GenaroRdz/International-Power-and-Grid-Management/Neurnal-Network/train/Hyundai/Hyundai_005.jpg

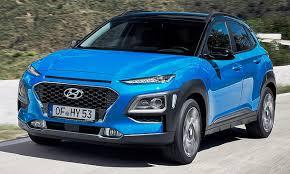
Neurnal-Network/train/Hyundai/Hyundai_005.jpg
