GenaroRdz/International-Power-and-Grid-Management/Neurnal-Network/train/MG/MG_098.jpg

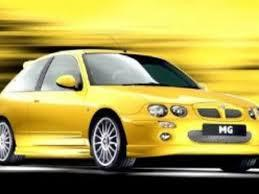
Neurnal-Network/train/MG/MG_098.jpg
