GenaroRdz/International-Power-and-Grid-Management/Neurnal-Network/graficas/mlp_size_vs_accuracy.png

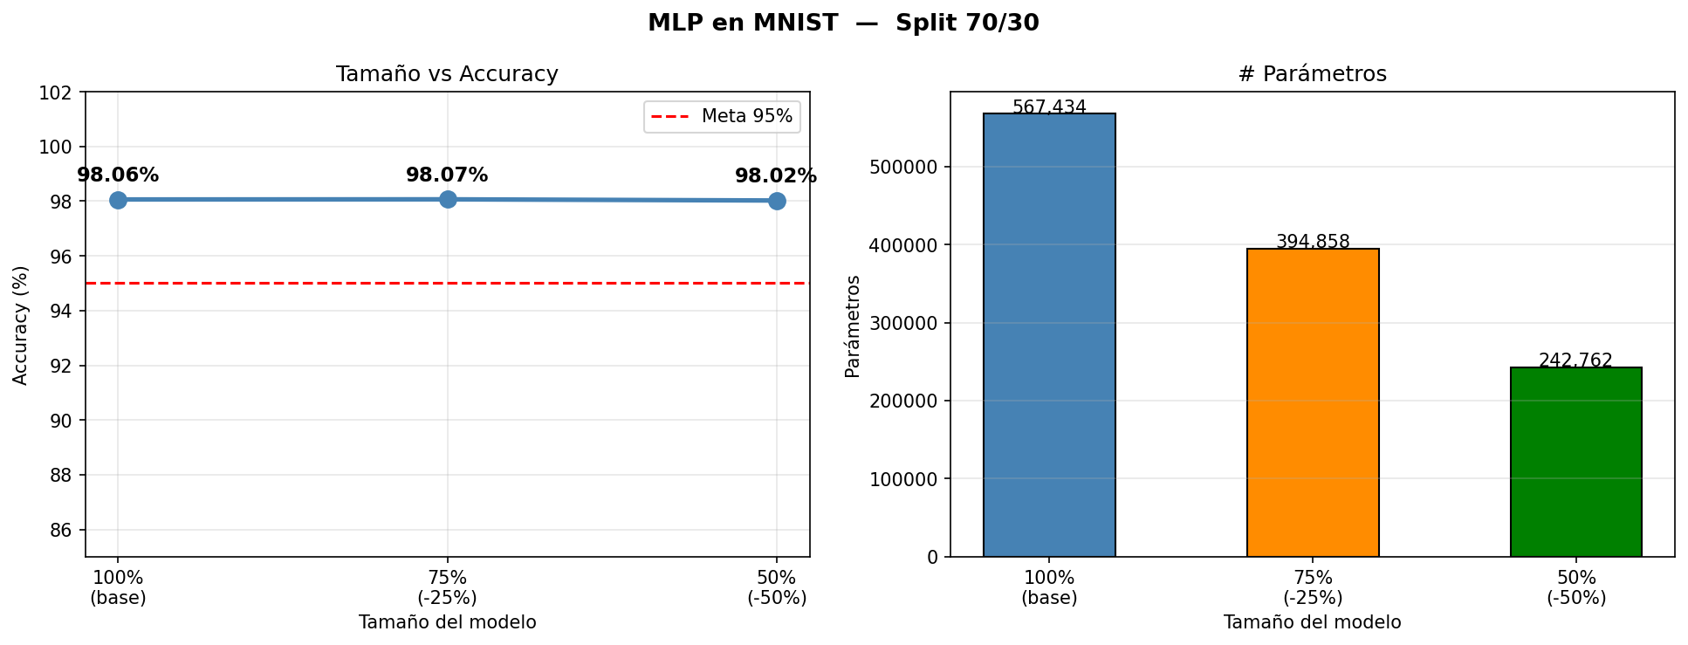
Neurnal-Network/graficas/mlp_size_vs_accuracy.png
