GenaroRdz/International-Power-and-Grid-Management/Neurnal-Network/train/Acura/Acura_019.jpg

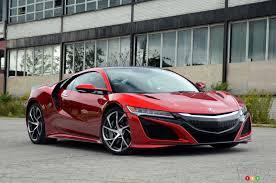
Neurnal-Network/train/Acura/Acura_019.jpg
