GenaroRdz/International-Power-and-Grid-Management/Neurnal-Network/train/Acura/Acura_023.jpg

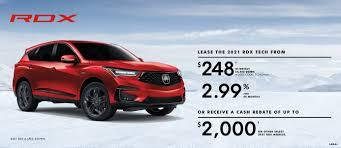
Neurnal-Network/train/Acura/Acura_023.jpg
