GenaroRdz/International-Power-and-Grid-Management/Neurnal-Network/train/Acura/Acura_026.jpg

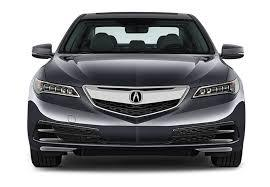
Neurnal-Network/train/Acura/Acura_026.jpg
