GenaroRdz/International-Power-and-Grid-Management/Neurnal-Network/train/Acura/Acura_050.jpg

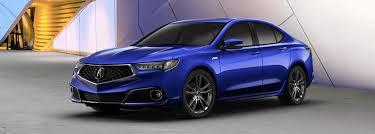
Neurnal-Network/train/Acura/Acura_050.jpg
