GenaroRdz/International-Power-and-Grid-Management/Neurnal-Network/train/Acura/Acura_061.jpg

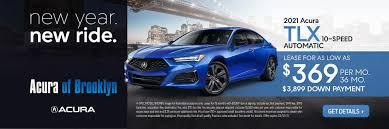
Neurnal-Network/train/Acura/Acura_061.jpg
