GenaroRdz/International-Power-and-Grid-Management/Neurnal-Network/train/Acura/Acura_066.jpg

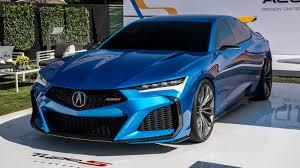
Neurnal-Network/train/Acura/Acura_066.jpg
