GenaroRdz/International-Power-and-Grid-Management/Neurnal-Network/train/Acura/Acura_078.jpg

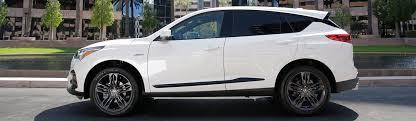
Neurnal-Network/train/Acura/Acura_078.jpg
