GenaroRdz/International-Power-and-Grid-Management/Neurnal-Network/train/Acura/Acura_080.jpg

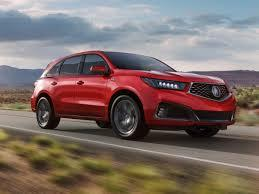
Neurnal-Network/train/Acura/Acura_080.jpg
