GenaroRdz/International-Power-and-Grid-Management/Neurnal-Network/train/Acura/Acura_088.jpg

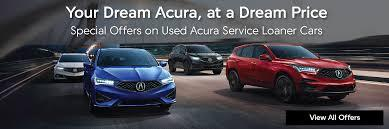
Neurnal-Network/train/Acura/Acura_088.jpg
