GenaroRdz/International-Power-and-Grid-Management/Neurnal-Network/train/Alfa Romeo/Alfa Romeo_034.jpg

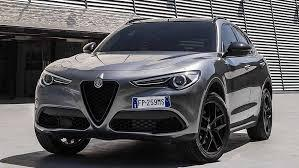
Neurnal-Network/train/Alfa Romeo/Alfa Romeo_034.jpg
