GenaroRdz/International-Power-and-Grid-Management/Neurnal-Network/train/Alfa Romeo/Alfa Romeo_074.jpg

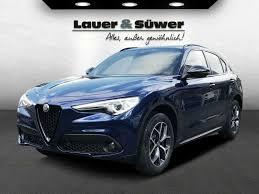
Neurnal-Network/train/Alfa Romeo/Alfa Romeo_074.jpg
