GenaroRdz/International-Power-and-Grid-Management/Neurnal-Network/train/Aston Martin/Aston Martin_030.jpg

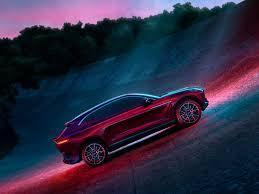
Neurnal-Network/train/Aston Martin/Aston Martin_030.jpg
