GenaroRdz/International-Power-and-Grid-Management/Neurnal-Network/train/Audi/Audi_017.jpg

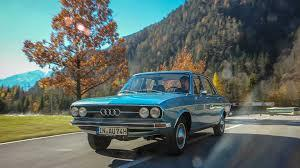
Neurnal-Network/train/Audi/Audi_017.jpg
