GenaroRdz/International-Power-and-Grid-Management/Neurnal-Network/train/Audi/Audi_038.jpg

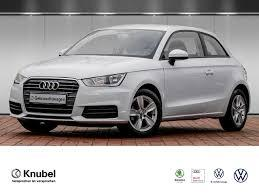
Neurnal-Network/train/Audi/Audi_038.jpg
