GenaroRdz/International-Power-and-Grid-Management/Neurnal-Network/train/Audi/Audi_059.jpg

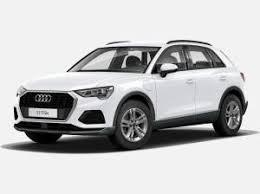
Neurnal-Network/train/Audi/Audi_059.jpg
