GenaroRdz/International-Power-and-Grid-Management/Neurnal-Network/train/Bentley/Bentley_013.jpg

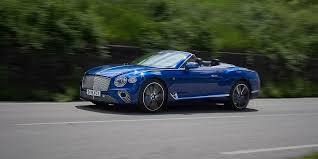
Neurnal-Network/train/Bentley/Bentley_013.jpg
