GenaroRdz/International-Power-and-Grid-Management/Neurnal-Network/train/Bentley/Bentley_045.jpg

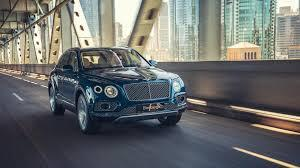
Neurnal-Network/train/Bentley/Bentley_045.jpg
