GenaroRdz/International-Power-and-Grid-Management/Neurnal-Network/train/Bentley/Bentley_058.jpg

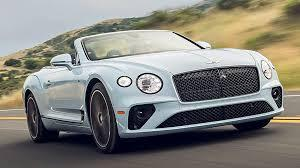
Neurnal-Network/train/Bentley/Bentley_058.jpg
