GenaroRdz/International-Power-and-Grid-Management/Neurnal-Network/train/Bentley/Bentley_075.jpg

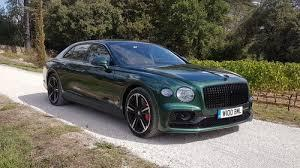
Neurnal-Network/train/Bentley/Bentley_075.jpg
