GenaroRdz/International-Power-and-Grid-Management/Neurnal-Network/train/BMW/BMW_029.jpg

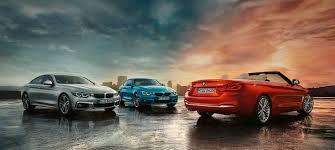
Neurnal-Network/train/BMW/BMW_029.jpg
