GenaroRdz/International-Power-and-Grid-Management/Neurnal-Network/train/BMW/BMW_037.jpg

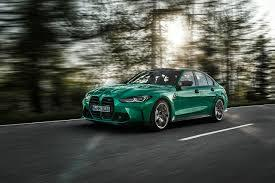
Neurnal-Network/train/BMW/BMW_037.jpg
