GenaroRdz/International-Power-and-Grid-Management/Neurnal-Network/train/BMW/BMW_071.jpg

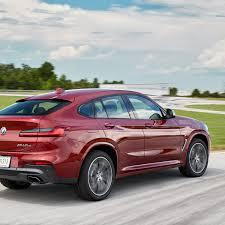
Neurnal-Network/train/BMW/BMW_071.jpg
