GenaroRdz/International-Power-and-Grid-Management/Neurnal-Network/train/Bugatti/Bugatti_005.jpg

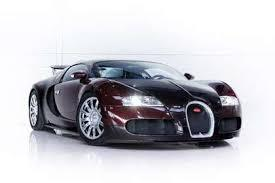
Neurnal-Network/train/Bugatti/Bugatti_005.jpg
