GenaroRdz/International-Power-and-Grid-Management/Neurnal-Network/train/Bugatti/Bugatti_016.jpg

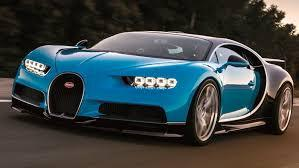
Neurnal-Network/train/Bugatti/Bugatti_016.jpg
