GenaroRdz/International-Power-and-Grid-Management/Neurnal-Network/train/Bugatti/Bugatti_018.jpg

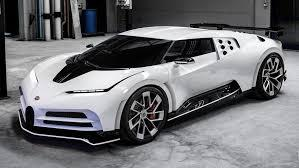
Neurnal-Network/train/Bugatti/Bugatti_018.jpg
