GenaroRdz/International-Power-and-Grid-Management/Neurnal-Network/train/Bugatti/Bugatti_038.jpg

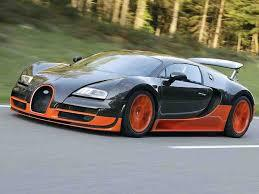
Neurnal-Network/train/Bugatti/Bugatti_038.jpg
