GenaroRdz/International-Power-and-Grid-Management/Neurnal-Network/train/Bugatti/Bugatti_048.jpg

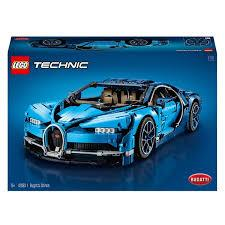
Neurnal-Network/train/Bugatti/Bugatti_048.jpg
