GenaroRdz/International-Power-and-Grid-Management/Neurnal-Network/train/Bugatti/Bugatti_087.jpg

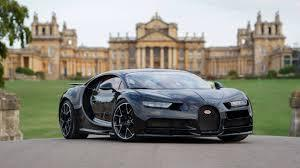
Neurnal-Network/train/Bugatti/Bugatti_087.jpg
