GenaroRdz/International-Power-and-Grid-Management/Neurnal-Network/train/Buick/Buick_023.jpg

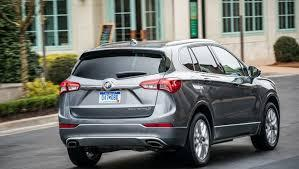
Neurnal-Network/train/Buick/Buick_023.jpg
