GenaroRdz/International-Power-and-Grid-Management/Neurnal-Network/train/Buick/Buick_024.jpg

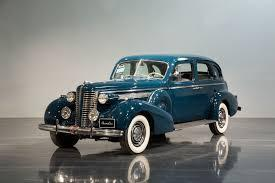
Neurnal-Network/train/Buick/Buick_024.jpg
