GenaroRdz/International-Power-and-Grid-Management/Neurnal-Network/train/Buick/Buick_026.jpg

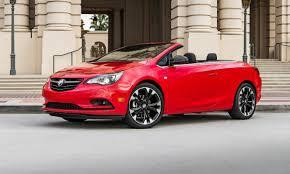
Neurnal-Network/train/Buick/Buick_026.jpg
