GenaroRdz/International-Power-and-Grid-Management/Neurnal-Network/train/Buick/Buick_034.jpg

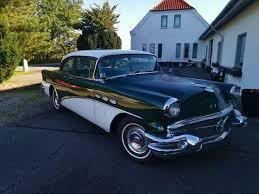
Neurnal-Network/train/Buick/Buick_034.jpg
