GenaroRdz/International-Power-and-Grid-Management/Neurnal-Network/train/Buick/Buick_044.jpg

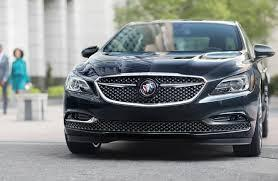
Neurnal-Network/train/Buick/Buick_044.jpg
