GenaroRdz/International-Power-and-Grid-Management/Neurnal-Network/train/Buick/Buick_053.jpg

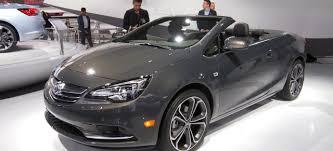
Neurnal-Network/train/Buick/Buick_053.jpg
