GenaroRdz/International-Power-and-Grid-Management/Neurnal-Network/train/Buick/Buick_087.jpg

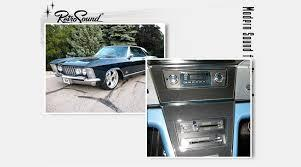
Neurnal-Network/train/Buick/Buick_087.jpg
