GenaroRdz/International-Power-and-Grid-Management/Neurnal-Network/train/Buick/Buick_091.jpg

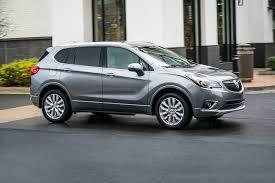
Neurnal-Network/train/Buick/Buick_091.jpg
