GenaroRdz/International-Power-and-Grid-Management/Neurnal-Network/train/Cadillac/Cadillac_010.jpg

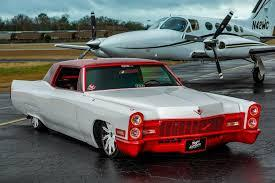
Neurnal-Network/train/Cadillac/Cadillac_010.jpg
