GenaroRdz/International-Power-and-Grid-Management/Neurnal-Network/train/Cadillac/Cadillac_023.jpg

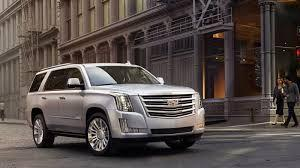
Neurnal-Network/train/Cadillac/Cadillac_023.jpg
