GenaroRdz/International-Power-and-Grid-Management/Neurnal-Network/train/Cadillac/Cadillac_036.jpg

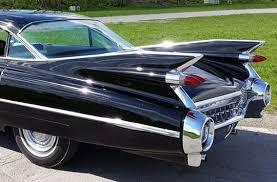
Neurnal-Network/train/Cadillac/Cadillac_036.jpg
