GenaroRdz/International-Power-and-Grid-Management/Neurnal-Network/train/Cadillac/Cadillac_062.jpg

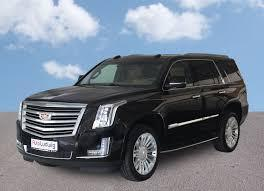
Neurnal-Network/train/Cadillac/Cadillac_062.jpg
