GenaroRdz/International-Power-and-Grid-Management/Neurnal-Network/train/Cadillac/Cadillac_063.jpg

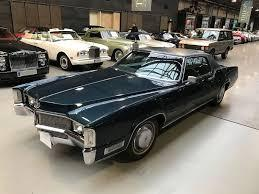
Neurnal-Network/train/Cadillac/Cadillac_063.jpg
