GenaroRdz/International-Power-and-Grid-Management/Neurnal-Network/train/Cadillac/Cadillac_084.jpg

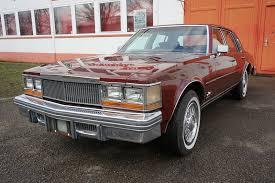
Neurnal-Network/train/Cadillac/Cadillac_084.jpg
