GenaroRdz/International-Power-and-Grid-Management/Neurnal-Network/train/Chevrolet/Chevrolet_023.jpg

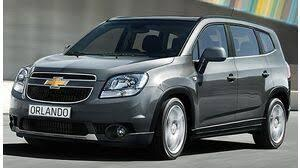
Neurnal-Network/train/Chevrolet/Chevrolet_023.jpg
