GenaroRdz/International-Power-and-Grid-Management/Neurnal-Network/train/Chevrolet/Chevrolet_030.jpg

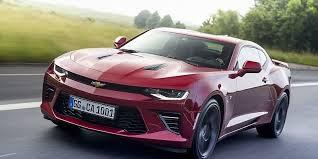
Neurnal-Network/train/Chevrolet/Chevrolet_030.jpg
