GenaroRdz/International-Power-and-Grid-Management/Neurnal-Network/train/Chevrolet/Chevrolet_035.jpg

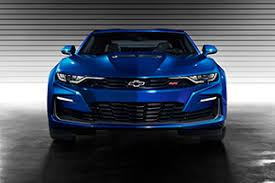
Neurnal-Network/train/Chevrolet/Chevrolet_035.jpg
