GenaroRdz/International-Power-and-Grid-Management/Neurnal-Network/train/Chevrolet/Chevrolet_060.jpg

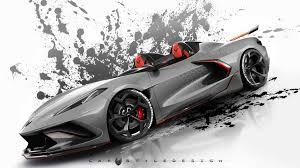
Neurnal-Network/train/Chevrolet/Chevrolet_060.jpg
