GenaroRdz/International-Power-and-Grid-Management/Neurnal-Network/train/Chevrolet/Chevrolet_083.jpg

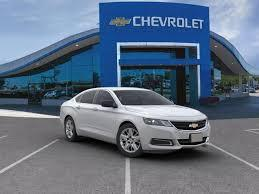
Neurnal-Network/train/Chevrolet/Chevrolet_083.jpg
