GenaroRdz/International-Power-and-Grid-Management/Neurnal-Network/train/Chevrolet/Chevrolet_084.jpg

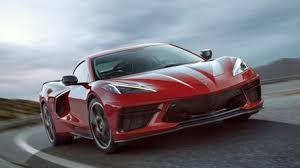
Neurnal-Network/train/Chevrolet/Chevrolet_084.jpg
