GenaroRdz/International-Power-and-Grid-Management/Neurnal-Network/train/Chrysler/Chrysler_004.jpg

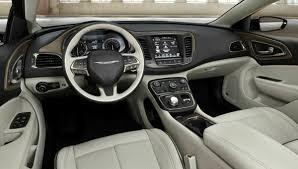
Neurnal-Network/train/Chrysler/Chrysler_004.jpg
