GenaroRdz/International-Power-and-Grid-Management/Neurnal-Network/train/Chrysler/Chrysler_086.jpg

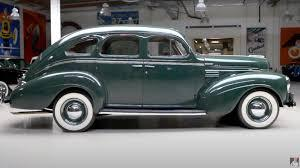
Neurnal-Network/train/Chrysler/Chrysler_086.jpg
