GenaroRdz/International-Power-and-Grid-Management/Neurnal-Network/train/Citroen/Citroen_018.jpg

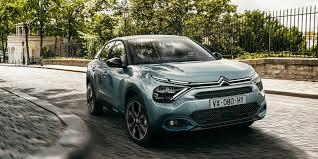
Neurnal-Network/train/Citroen/Citroen_018.jpg
