GenaroRdz/International-Power-and-Grid-Management/Neurnal-Network/train/Citroen/Citroen_023.jpg

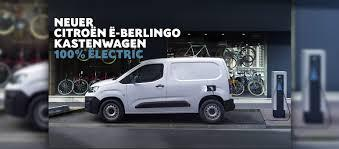
Neurnal-Network/train/Citroen/Citroen_023.jpg
