GenaroRdz/International-Power-and-Grid-Management/Neurnal-Network/train/Citroen/Citroen_032.jpg

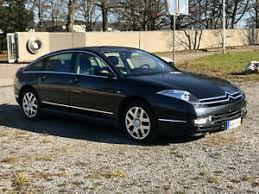
Neurnal-Network/train/Citroen/Citroen_032.jpg
