GenaroRdz/International-Power-and-Grid-Management/Neurnal-Network/train/Citroen/Citroen_034.jpg

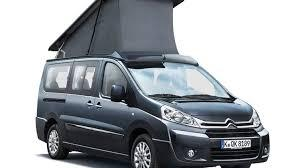
Neurnal-Network/train/Citroen/Citroen_034.jpg
