GenaroRdz/International-Power-and-Grid-Management/Neurnal-Network/train/Citroen/Citroen_036.jpg

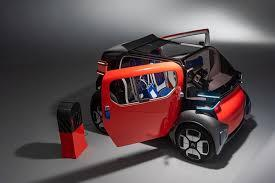
Neurnal-Network/train/Citroen/Citroen_036.jpg
