GenaroRdz/International-Power-and-Grid-Management/Neurnal-Network/train/Citroen/Citroen_077.jpg

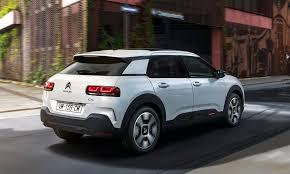
Neurnal-Network/train/Citroen/Citroen_077.jpg
