GenaroRdz/International-Power-and-Grid-Management/Neurnal-Network/train/Citroen/Citroen_078.jpg

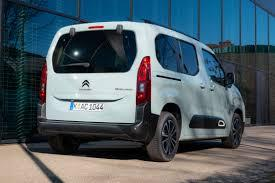
Neurnal-Network/train/Citroen/Citroen_078.jpg
