GenaroRdz/International-Power-and-Grid-Management/Neurnal-Network/train/Daewoo/Daewoo_008.jpg

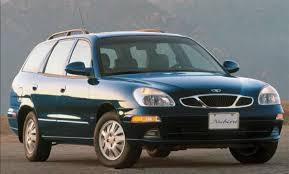
Neurnal-Network/train/Daewoo/Daewoo_008.jpg
