GenaroRdz/International-Power-and-Grid-Management/Neurnal-Network/train/Daewoo/Daewoo_037.jpg

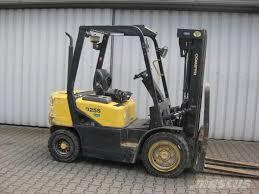
Neurnal-Network/train/Daewoo/Daewoo_037.jpg
