GenaroRdz/International-Power-and-Grid-Management/Neurnal-Network/train/Daewoo/Daewoo_059.jpg

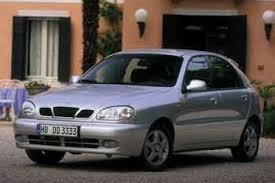
Neurnal-Network/train/Daewoo/Daewoo_059.jpg
