GenaroRdz/International-Power-and-Grid-Management/Neurnal-Network/train/Daewoo/Daewoo_086.jpg

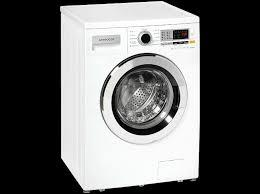
Neurnal-Network/train/Daewoo/Daewoo_086.jpg
