GenaroRdz/International-Power-and-Grid-Management/Neurnal-Network/train/Daewoo/Daewoo_088.jpg

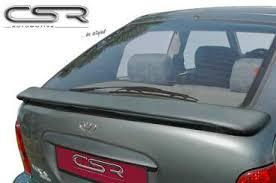
Neurnal-Network/train/Daewoo/Daewoo_088.jpg
