GenaroRdz/International-Power-and-Grid-Management/Neurnal-Network/train/Dodge/Dodge_002.jpg

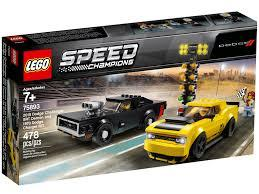
Neurnal-Network/train/Dodge/Dodge_002.jpg
