GenaroRdz/International-Power-and-Grid-Management/Neurnal-Network/train/Dodge/Dodge_019.jpg

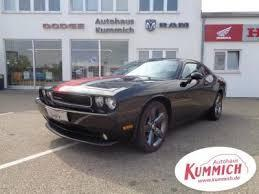
Neurnal-Network/train/Dodge/Dodge_019.jpg
