GenaroRdz/International-Power-and-Grid-Management/Neurnal-Network/train/Dodge/Dodge_027.jpg

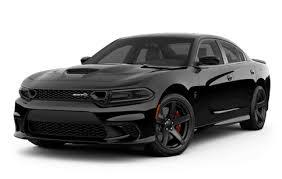
Neurnal-Network/train/Dodge/Dodge_027.jpg
