GenaroRdz/International-Power-and-Grid-Management/Neurnal-Network/train/Dodge/Dodge_032.jpg

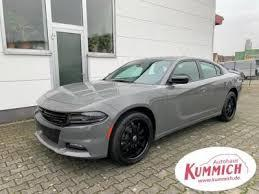
Neurnal-Network/train/Dodge/Dodge_032.jpg
