GenaroRdz/International-Power-and-Grid-Management/Neurnal-Network/train/Dodge/Dodge_049.jpg

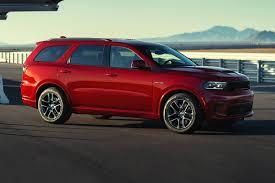
Neurnal-Network/train/Dodge/Dodge_049.jpg
