GenaroRdz/International-Power-and-Grid-Management/Neurnal-Network/train/Dodge/Dodge_055.jpg

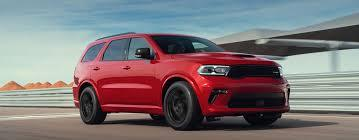
Neurnal-Network/train/Dodge/Dodge_055.jpg
