GenaroRdz/International-Power-and-Grid-Management/Neurnal-Network/train/Dodge/Dodge_057.jpg

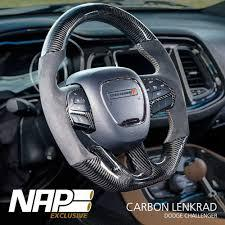
Neurnal-Network/train/Dodge/Dodge_057.jpg
