GenaroRdz/International-Power-and-Grid-Management/Neurnal-Network/train/Dodge/Dodge_060.jpg

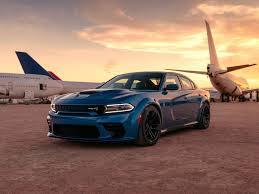
Neurnal-Network/train/Dodge/Dodge_060.jpg
