GenaroRdz/International-Power-and-Grid-Management/Neurnal-Network/train/Dodge/Dodge_066.jpg

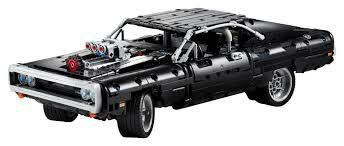
Neurnal-Network/train/Dodge/Dodge_066.jpg
