GenaroRdz/International-Power-and-Grid-Management/Neurnal-Network/train/Dodge/Dodge_072.jpg

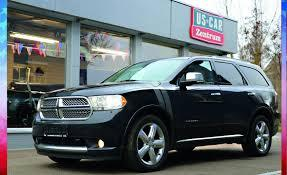
Neurnal-Network/train/Dodge/Dodge_072.jpg
