GenaroRdz/International-Power-and-Grid-Management/Neurnal-Network/train/Ferrari/Ferrari_000.jpg

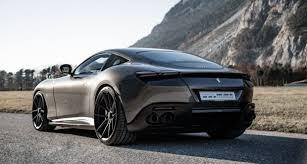
Neurnal-Network/train/Ferrari/Ferrari_000.jpg
