GenaroRdz/International-Power-and-Grid-Management/Neurnal-Network/train/Ferrari/Ferrari_005.jpg

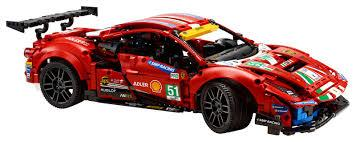
Neurnal-Network/train/Ferrari/Ferrari_005.jpg
