GenaroRdz/International-Power-and-Grid-Management/Neurnal-Network/train/Ferrari/Ferrari_023.jpg

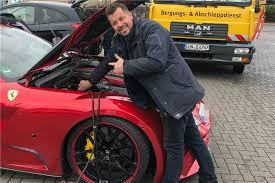
Neurnal-Network/train/Ferrari/Ferrari_023.jpg
