GenaroRdz/International-Power-and-Grid-Management/Neurnal-Network/train/Ferrari/Ferrari_039.jpg

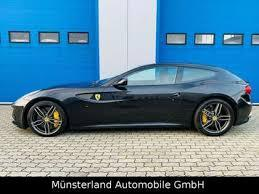
Neurnal-Network/train/Ferrari/Ferrari_039.jpg
