GenaroRdz/International-Power-and-Grid-Management/Neurnal-Network/train/Ferrari/Ferrari_059.jpg

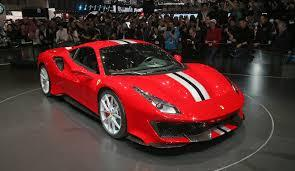
Neurnal-Network/train/Ferrari/Ferrari_059.jpg
