GenaroRdz/International-Power-and-Grid-Management/Neurnal-Network/train/Ferrari/Ferrari_069.jpg

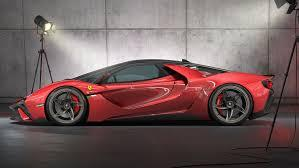
Neurnal-Network/train/Ferrari/Ferrari_069.jpg
