GenaroRdz/International-Power-and-Grid-Management/Neurnal-Network/train/Ferrari/Ferrari_077.jpg

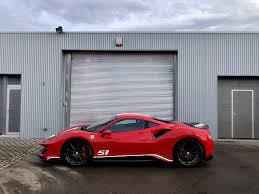
Neurnal-Network/train/Ferrari/Ferrari_077.jpg
