GenaroRdz/International-Power-and-Grid-Management/Neurnal-Network/train/Ferrari/Ferrari_082.jpg

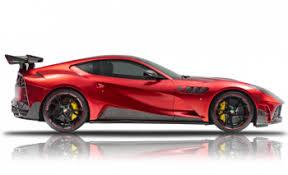
Neurnal-Network/train/Ferrari/Ferrari_082.jpg
