GenaroRdz/International-Power-and-Grid-Management/Neurnal-Network/train/Fiat/Fiat_014.jpg

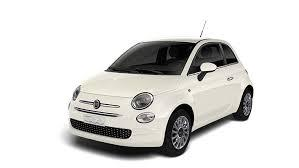
Neurnal-Network/train/Fiat/Fiat_014.jpg
