GenaroRdz/International-Power-and-Grid-Management/Neurnal-Network/train/Fiat/Fiat_042.jpg

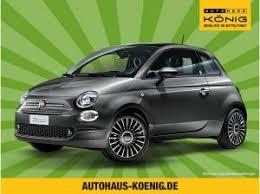
Neurnal-Network/train/Fiat/Fiat_042.jpg
