GenaroRdz/International-Power-and-Grid-Management/Neurnal-Network/train/Fiat/Fiat_068.jpg

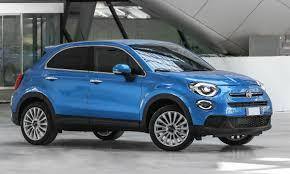
Neurnal-Network/train/Fiat/Fiat_068.jpg
