GenaroRdz/International-Power-and-Grid-Management/Neurnal-Network/train/Fiat/Fiat_070.jpg

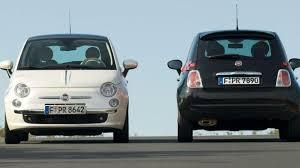
Neurnal-Network/train/Fiat/Fiat_070.jpg
