GenaroRdz/International-Power-and-Grid-Management/Neurnal-Network/train/Fiat/Fiat_072.jpg

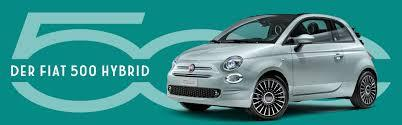
Neurnal-Network/train/Fiat/Fiat_072.jpg
