GenaroRdz/International-Power-and-Grid-Management/Neurnal-Network/train/Fiat/Fiat_080.jpg

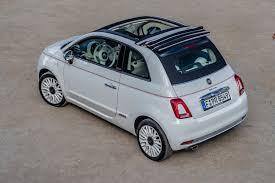
Neurnal-Network/train/Fiat/Fiat_080.jpg
