GenaroRdz/International-Power-and-Grid-Management/Neurnal-Network/train/Ford/Ford_022.jpg

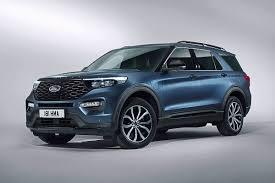
Neurnal-Network/train/Ford/Ford_022.jpg
