GenaroRdz/International-Power-and-Grid-Management/Neurnal-Network/train/Ford/Ford_027.jpg

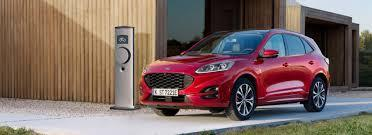
Neurnal-Network/train/Ford/Ford_027.jpg
