GenaroRdz/International-Power-and-Grid-Management/Neurnal-Network/train/Ford/Ford_031.jpg

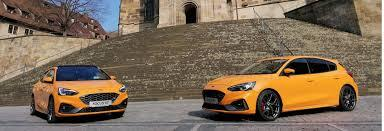
Neurnal-Network/train/Ford/Ford_031.jpg
