GenaroRdz/International-Power-and-Grid-Management/Neurnal-Network/train/Ford/Ford_050.jpg

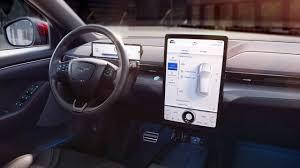
Neurnal-Network/train/Ford/Ford_050.jpg
