GenaroRdz/International-Power-and-Grid-Management/Neurnal-Network/train/Ford/Ford_054.jpg

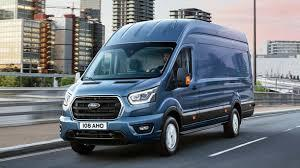
Neurnal-Network/train/Ford/Ford_054.jpg
