GenaroRdz/International-Power-and-Grid-Management/Neurnal-Network/train/Ford/Ford_065.jpg

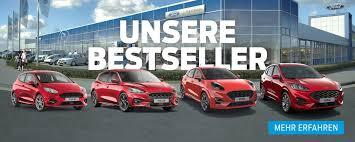
Neurnal-Network/train/Ford/Ford_065.jpg
