GenaroRdz/International-Power-and-Grid-Management/Neurnal-Network/train/Ford/Ford_080.jpg

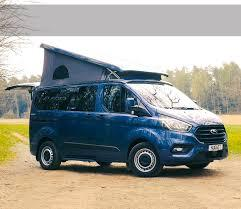
Neurnal-Network/train/Ford/Ford_080.jpg
