GenaroRdz/International-Power-and-Grid-Management/Neurnal-Network/train/Genesis/Genesis_043.jpg

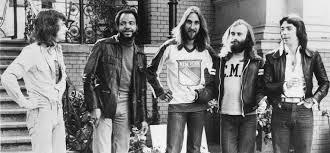
Neurnal-Network/train/Genesis/Genesis_043.jpg
