GenaroRdz/International-Power-and-Grid-Management/Neurnal-Network/train/GMC/GMC_002.jpg

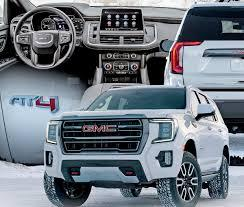
Neurnal-Network/train/GMC/GMC_002.jpg
