GenaroRdz/International-Power-and-Grid-Management/Neurnal-Network/train/GMC/GMC_004.jpg

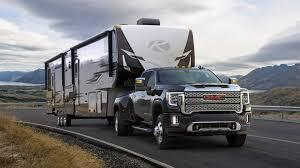
Neurnal-Network/train/GMC/GMC_004.jpg
