GenaroRdz/International-Power-and-Grid-Management/Neurnal-Network/train/GMC/GMC_021.jpg

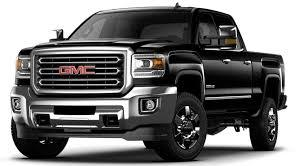
Neurnal-Network/train/GMC/GMC_021.jpg
