GenaroRdz/International-Power-and-Grid-Management/Neurnal-Network/train/GMC/GMC_039.jpg

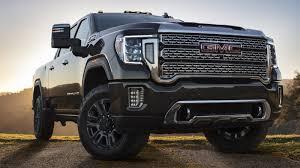
Neurnal-Network/train/GMC/GMC_039.jpg
