GenaroRdz/International-Power-and-Grid-Management/Neurnal-Network/train/GMC/GMC_041.jpg

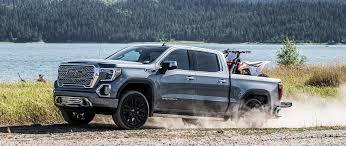
Neurnal-Network/train/GMC/GMC_041.jpg
