GenaroRdz/International-Power-and-Grid-Management/Neurnal-Network/train/GMC/GMC_050.jpg

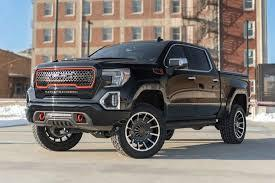
Neurnal-Network/train/GMC/GMC_050.jpg
