GenaroRdz/International-Power-and-Grid-Management/Neurnal-Network/train/GMC/GMC_064.jpg

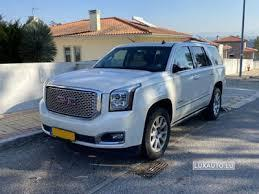
Neurnal-Network/train/GMC/GMC_064.jpg
