GenaroRdz/International-Power-and-Grid-Management/Neurnal-Network/train/GMC/GMC_081.jpg

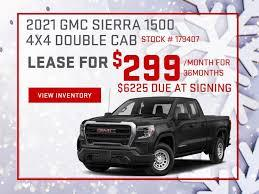
Neurnal-Network/train/GMC/GMC_081.jpg
