GenaroRdz/International-Power-and-Grid-Management/Neurnal-Network/train/Honda/Honda_001.jpg

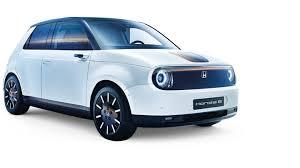
Neurnal-Network/train/Honda/Honda_001.jpg
