GenaroRdz/International-Power-and-Grid-Management/Neurnal-Network/train/Honda/Honda_010.jpg

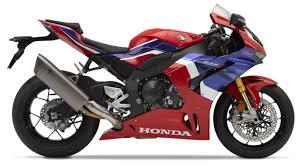
Neurnal-Network/train/Honda/Honda_010.jpg
