GenaroRdz/International-Power-and-Grid-Management/Neurnal-Network/train/Honda/Honda_032.jpg

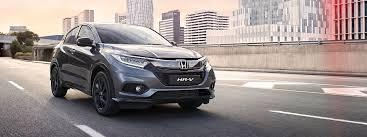
Neurnal-Network/train/Honda/Honda_032.jpg
