GenaroRdz/International-Power-and-Grid-Management/Neurnal-Network/train/Honda/Honda_036.jpg

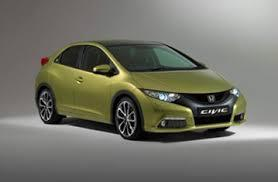
Neurnal-Network/train/Honda/Honda_036.jpg
