GenaroRdz/International-Power-and-Grid-Management/Neurnal-Network/train/Honda/Honda_041.jpg

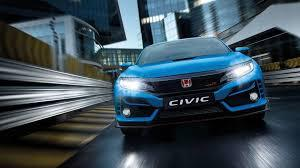
Neurnal-Network/train/Honda/Honda_041.jpg
