GenaroRdz/International-Power-and-Grid-Management/Neurnal-Network/train/Honda/Honda_048.jpg

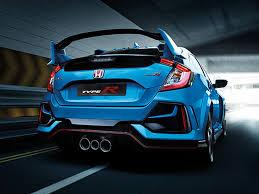
Neurnal-Network/train/Honda/Honda_048.jpg
