GenaroRdz/International-Power-and-Grid-Management/Neurnal-Network/train/Honda/Honda_058.jpg

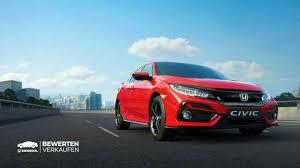
Neurnal-Network/train/Honda/Honda_058.jpg
