GenaroRdz/International-Power-and-Grid-Management/Neurnal-Network/train/Honda/Honda_078.jpg

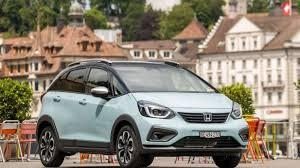
Neurnal-Network/train/Honda/Honda_078.jpg
