GenaroRdz/International-Power-and-Grid-Management/Neurnal-Network/train/Hudson/Hudson_018.jpg

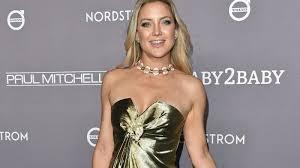
Neurnal-Network/train/Hudson/Hudson_018.jpg
