GenaroRdz/International-Power-and-Grid-Management/Neurnal-Network/train/Hudson/Hudson_065.jpg

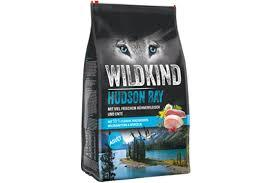
Neurnal-Network/train/Hudson/Hudson_065.jpg
