GenaroRdz/International-Power-and-Grid-Management/Neurnal-Network/train/Hudson/Hudson_069.jpg

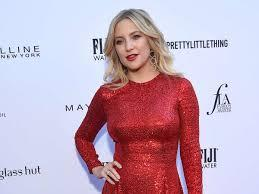
Neurnal-Network/train/Hudson/Hudson_069.jpg
