GenaroRdz/International-Power-and-Grid-Management/Neurnal-Network/train/Hudson/Hudson_096.jpg

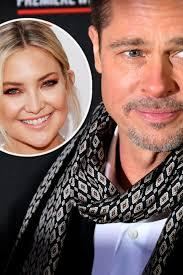
Neurnal-Network/train/Hudson/Hudson_096.jpg
