GenaroRdz/International-Power-and-Grid-Management/Neurnal-Network/train/Hudson/Hudson_099.jpg

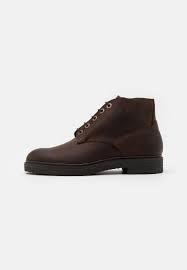
Neurnal-Network/train/Hudson/Hudson_099.jpg
