GenaroRdz/International-Power-and-Grid-Management/Neurnal-Network/train/Hyundai/Hyundai_013.jpg

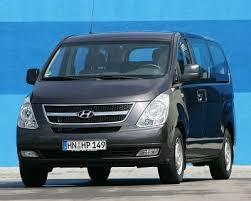
Neurnal-Network/train/Hyundai/Hyundai_013.jpg
