GenaroRdz/International-Power-and-Grid-Management/Neurnal-Network/train/Hyundai/Hyundai_016.jpg

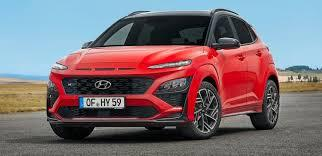
Neurnal-Network/train/Hyundai/Hyundai_016.jpg
