GenaroRdz/International-Power-and-Grid-Management/Neurnal-Network/train/Hyundai/Hyundai_019.jpg

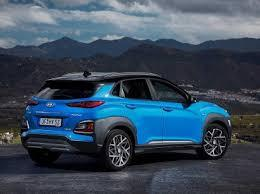
Neurnal-Network/train/Hyundai/Hyundai_019.jpg
