GenaroRdz/International-Power-and-Grid-Management/Neurnal-Network/train/Hyundai/Hyundai_027.jpg

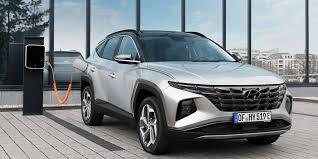
Neurnal-Network/train/Hyundai/Hyundai_027.jpg
