GenaroRdz/International-Power-and-Grid-Management/Neurnal-Network/train/Hyundai/Hyundai_038.jpg

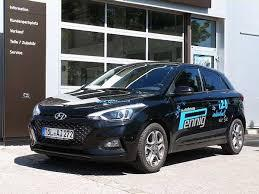
Neurnal-Network/train/Hyundai/Hyundai_038.jpg
