GenaroRdz/International-Power-and-Grid-Management/Neurnal-Network/train/Hyundai/Hyundai_069.jpg

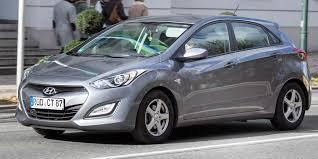
Neurnal-Network/train/Hyundai/Hyundai_069.jpg
