GenaroRdz/International-Power-and-Grid-Management/Neurnal-Network/train/Infiniti/Infiniti_009.jpg

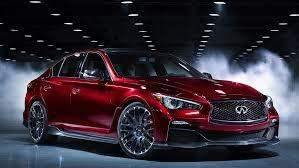
Neurnal-Network/train/Infiniti/Infiniti_009.jpg
