GenaroRdz/International-Power-and-Grid-Management/Neurnal-Network/train/Infiniti/Infiniti_045.jpg

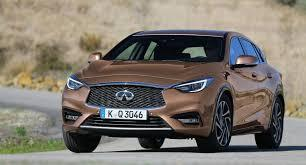
Neurnal-Network/train/Infiniti/Infiniti_045.jpg
