GenaroRdz/International-Power-and-Grid-Management/Neurnal-Network/train/Infiniti/Infiniti_047.jpg

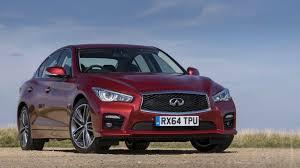
Neurnal-Network/train/Infiniti/Infiniti_047.jpg
