GenaroRdz/International-Power-and-Grid-Management/Neurnal-Network/train/Infiniti/Infiniti_061.jpg

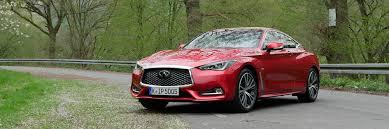
Neurnal-Network/train/Infiniti/Infiniti_061.jpg
