GenaroRdz/International-Power-and-Grid-Management/Neurnal-Network/train/Jaguar/Jaguar_007.jpg

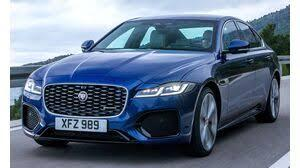
Neurnal-Network/train/Jaguar/Jaguar_007.jpg
