GenaroRdz/International-Power-and-Grid-Management/Neurnal-Network/train/Jaguar/Jaguar_011.jpg

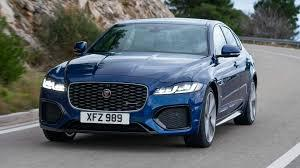
Neurnal-Network/train/Jaguar/Jaguar_011.jpg
