GenaroRdz/International-Power-and-Grid-Management/Neurnal-Network/train/Jaguar/Jaguar_020.jpg

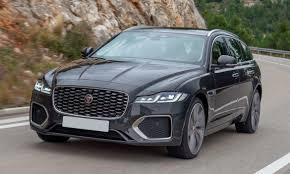
Neurnal-Network/train/Jaguar/Jaguar_020.jpg
