GenaroRdz/International-Power-and-Grid-Management/Neurnal-Network/train/Jaguar/Jaguar_040.jpg

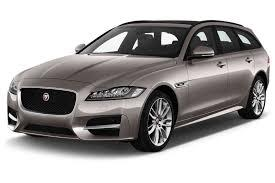
Neurnal-Network/train/Jaguar/Jaguar_040.jpg
