GenaroRdz/International-Power-and-Grid-Management/Neurnal-Network/train/Jaguar/Jaguar_046.jpg

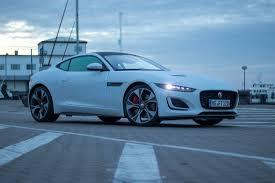
Neurnal-Network/train/Jaguar/Jaguar_046.jpg
