GenaroRdz/International-Power-and-Grid-Management/Neurnal-Network/train/Jeep/Jeep_020.jpg

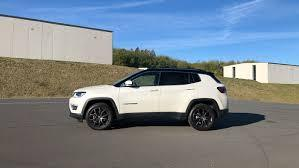
Neurnal-Network/train/Jeep/Jeep_020.jpg
