GenaroRdz/International-Power-and-Grid-Management/Neurnal-Network/train/Jeep/Jeep_029.jpg

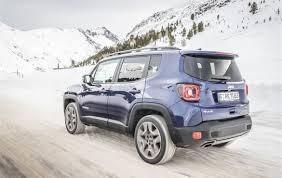
Neurnal-Network/train/Jeep/Jeep_029.jpg
