GenaroRdz/International-Power-and-Grid-Management/Neurnal-Network/train/Jeep/Jeep_048.jpg

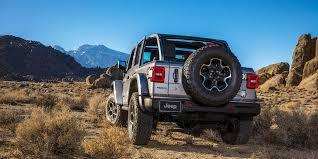
Neurnal-Network/train/Jeep/Jeep_048.jpg
