GenaroRdz/International-Power-and-Grid-Management/Neurnal-Network/train/Jeep/Jeep_066.jpg

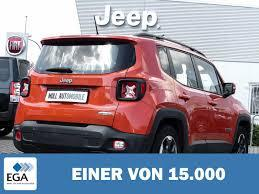
Neurnal-Network/train/Jeep/Jeep_066.jpg
