GenaroRdz/International-Power-and-Grid-Management/Neurnal-Network/train/Kia/Kia_004.jpg

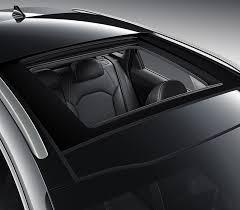
Neurnal-Network/train/Kia/Kia_004.jpg
