GenaroRdz/International-Power-and-Grid-Management/Neurnal-Network/train/Kia/Kia_028.jpg

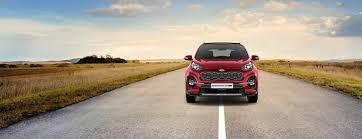
Neurnal-Network/train/Kia/Kia_028.jpg
