GenaroRdz/International-Power-and-Grid-Management/Neurnal-Network/train/Kia/Kia_033.jpg

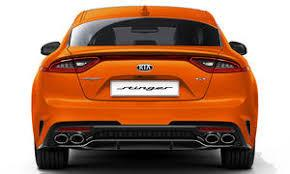
Neurnal-Network/train/Kia/Kia_033.jpg
