GenaroRdz/International-Power-and-Grid-Management/Neurnal-Network/train/Kia/Kia_042.jpg

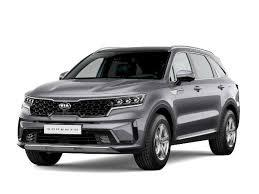
Neurnal-Network/train/Kia/Kia_042.jpg
