GenaroRdz/International-Power-and-Grid-Management/Neurnal-Network/train/Kia/Kia_058.jpg

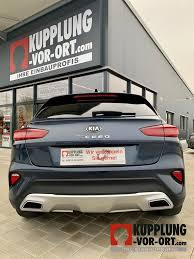
Neurnal-Network/train/Kia/Kia_058.jpg
