GenaroRdz/International-Power-and-Grid-Management/Neurnal-Network/train/Kia/Kia_061.jpg

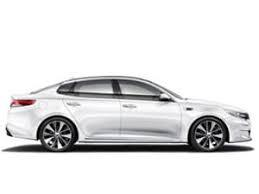
Neurnal-Network/train/Kia/Kia_061.jpg
