GenaroRdz/International-Power-and-Grid-Management/Neurnal-Network/train/Kia/Kia_065.jpg

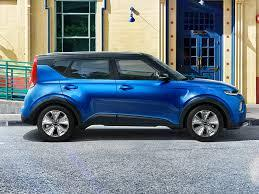
Neurnal-Network/train/Kia/Kia_065.jpg
