GenaroRdz/International-Power-and-Grid-Management/Neurnal-Network/train/Kia/Kia_079.jpg

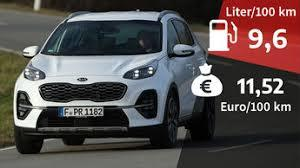
Neurnal-Network/train/Kia/Kia_079.jpg
