GenaroRdz/International-Power-and-Grid-Management/Neurnal-Network/train/Land Rover/Land Rover_026.jpg

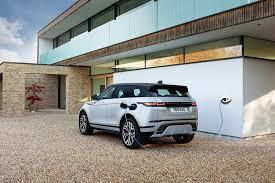
Neurnal-Network/train/Land Rover/Land Rover_026.jpg
