GenaroRdz/International-Power-and-Grid-Management/Neurnal-Network/train/Land Rover/Land Rover_036.jpg

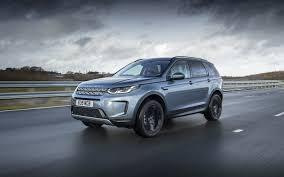
Neurnal-Network/train/Land Rover/Land Rover_036.jpg
