GenaroRdz/International-Power-and-Grid-Management/Neurnal-Network/train/Lexus/Lexus_007.jpg

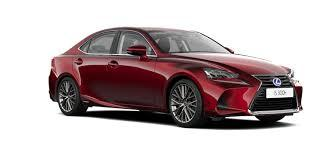
Neurnal-Network/train/Lexus/Lexus_007.jpg
