GenaroRdz/International-Power-and-Grid-Management/Neurnal-Network/train/Lexus/Lexus_008.jpg

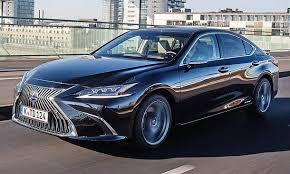
Neurnal-Network/train/Lexus/Lexus_008.jpg
