GenaroRdz/International-Power-and-Grid-Management/Neurnal-Network/train/Lexus/Lexus_024.jpg

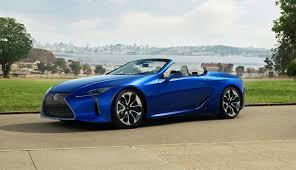
Neurnal-Network/train/Lexus/Lexus_024.jpg
