GenaroRdz/International-Power-and-Grid-Management/Neurnal-Network/train/Lexus/Lexus_027.jpg

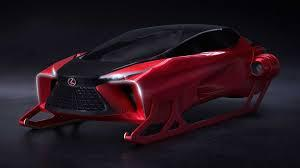
Neurnal-Network/train/Lexus/Lexus_027.jpg
