GenaroRdz/International-Power-and-Grid-Management/Neurnal-Network/train/Lexus/Lexus_052.jpg

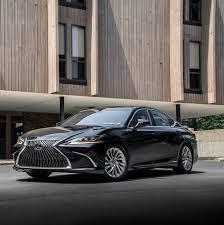
Neurnal-Network/train/Lexus/Lexus_052.jpg
