GenaroRdz/International-Power-and-Grid-Management/Neurnal-Network/train/Lexus/Lexus_055.jpg

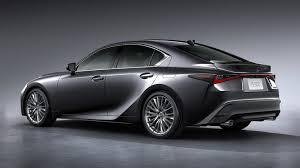
Neurnal-Network/train/Lexus/Lexus_055.jpg
