GenaroRdz/International-Power-and-Grid-Management/Neurnal-Network/train/Lexus/Lexus_072.jpg

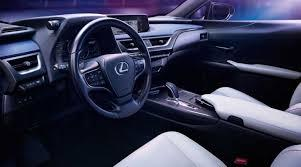
Neurnal-Network/train/Lexus/Lexus_072.jpg
