GenaroRdz/International-Power-and-Grid-Management/Neurnal-Network/train/Lexus/Lexus_082.jpg

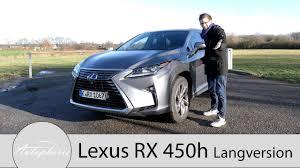
Neurnal-Network/train/Lexus/Lexus_082.jpg
