GenaroRdz/International-Power-and-Grid-Management/Neurnal-Network/train/Lincoln/Lincoln_025.jpg

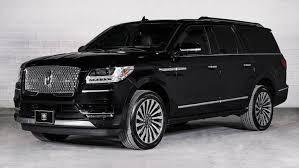
Neurnal-Network/train/Lincoln/Lincoln_025.jpg
