GenaroRdz/International-Power-and-Grid-Management/Neurnal-Network/train/Lincoln/Lincoln_032.jpg

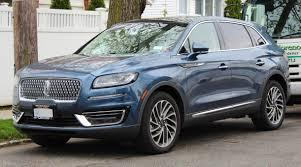
Neurnal-Network/train/Lincoln/Lincoln_032.jpg
