GenaroRdz/International-Power-and-Grid-Management/Neurnal-Network/train/Lincoln/Lincoln_058.jpg

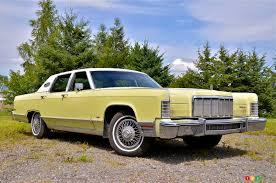
Neurnal-Network/train/Lincoln/Lincoln_058.jpg
