GenaroRdz/International-Power-and-Grid-Management/Neurnal-Network/train/Lincoln/Lincoln_059.jpg

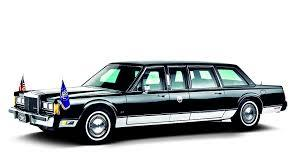
Neurnal-Network/train/Lincoln/Lincoln_059.jpg
