GenaroRdz/International-Power-and-Grid-Management/Neurnal-Network/train/Lincoln/Lincoln_076.jpg

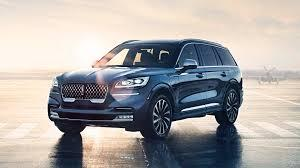
Neurnal-Network/train/Lincoln/Lincoln_076.jpg
