GenaroRdz/International-Power-and-Grid-Management/Neurnal-Network/train/Lincoln/Lincoln_077.jpg

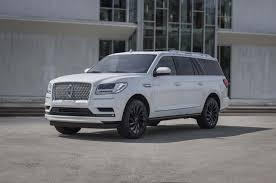
Neurnal-Network/train/Lincoln/Lincoln_077.jpg
