GenaroRdz/International-Power-and-Grid-Management/Neurnal-Network/train/Lincoln/Lincoln_083.jpg

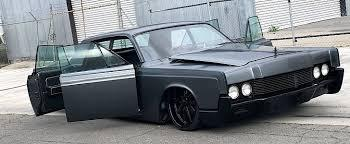
Neurnal-Network/train/Lincoln/Lincoln_083.jpg
