GenaroRdz/International-Power-and-Grid-Management/Neurnal-Network/train/Lincoln/Lincoln_091.jpg

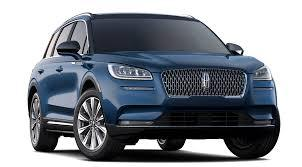
Neurnal-Network/train/Lincoln/Lincoln_091.jpg
