GenaroRdz/International-Power-and-Grid-Management/Neurnal-Network/train/Maserati/Maserati_013.jpg

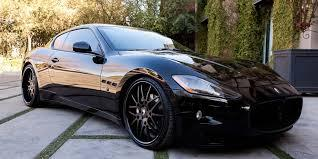
Neurnal-Network/train/Maserati/Maserati_013.jpg
