GenaroRdz/International-Power-and-Grid-Management/Neurnal-Network/train/Maserati/Maserati_025.jpg

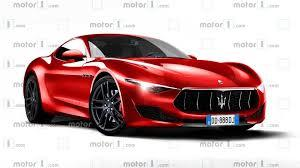
Neurnal-Network/train/Maserati/Maserati_025.jpg
