GenaroRdz/International-Power-and-Grid-Management/Neurnal-Network/train/Maserati/Maserati_028.jpg

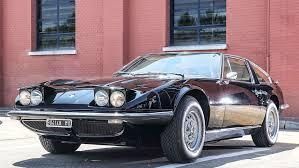
Neurnal-Network/train/Maserati/Maserati_028.jpg
