GenaroRdz/International-Power-and-Grid-Management/Neurnal-Network/train/Maserati/Maserati_046.jpg

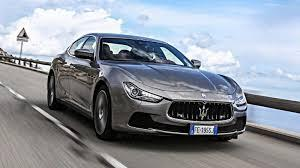
Neurnal-Network/train/Maserati/Maserati_046.jpg
