GenaroRdz/International-Power-and-Grid-Management/Neurnal-Network/train/Mazda/Mazda_011.jpg

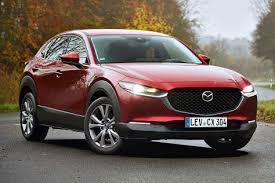
Neurnal-Network/train/Mazda/Mazda_011.jpg
