GenaroRdz/International-Power-and-Grid-Management/Neurnal-Network/train/Mazda/Mazda_020.jpg

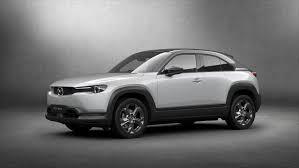
Neurnal-Network/train/Mazda/Mazda_020.jpg
