GenaroRdz/International-Power-and-Grid-Management/Neurnal-Network/train/Mazda/Mazda_049.jpg

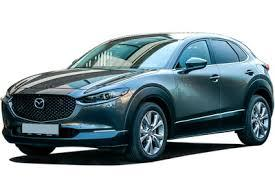
Neurnal-Network/train/Mazda/Mazda_049.jpg
