GenaroRdz/International-Power-and-Grid-Management/Neurnal-Network/train/Mazda/Mazda_054.jpg

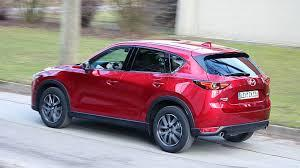
Neurnal-Network/train/Mazda/Mazda_054.jpg
