GenaroRdz/International-Power-and-Grid-Management/Neurnal-Network/train/Mazda/Mazda_057.jpg

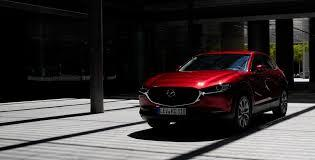
Neurnal-Network/train/Mazda/Mazda_057.jpg
