GenaroRdz/International-Power-and-Grid-Management/Neurnal-Network/train/Mercedes-Benz/Mercedes-Benz_015.jpg

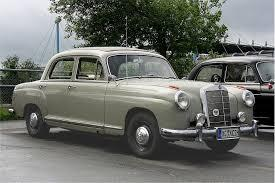
Neurnal-Network/train/Mercedes-Benz/Mercedes-Benz_015.jpg
