GenaroRdz/International-Power-and-Grid-Management/Neurnal-Network/train/MG/MG_033.jpg

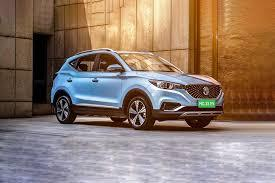
Neurnal-Network/train/MG/MG_033.jpg
