GenaroRdz/International-Power-and-Grid-Management/Neurnal-Network/train/MG/MG_044.jpg

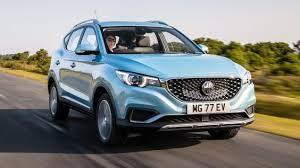
Neurnal-Network/train/MG/MG_044.jpg
