GenaroRdz/International-Power-and-Grid-Management/Neurnal-Network/train/MG/MG_047.jpg

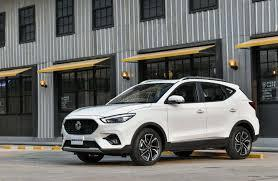
Neurnal-Network/train/MG/MG_047.jpg
