GenaroRdz/International-Power-and-Grid-Management/Neurnal-Network/train/MG/MG_060.jpg

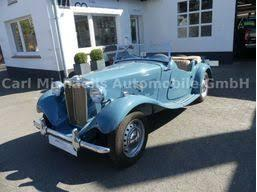
Neurnal-Network/train/MG/MG_060.jpg
