GenaroRdz/International-Power-and-Grid-Management/Neurnal-Network/train/MG/MG_087.jpg

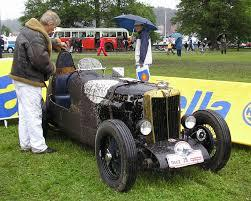
Neurnal-Network/train/MG/MG_087.jpg
