GenaroRdz/International-Power-and-Grid-Management/Neurnal-Network/train/MG/MG_093.jpg

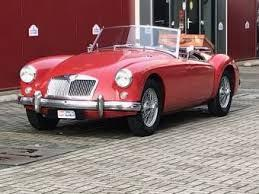
Neurnal-Network/train/MG/MG_093.jpg
