GenaroRdz/International-Power-and-Grid-Management/Neurnal-Network/train/MG/MG_118.jpg

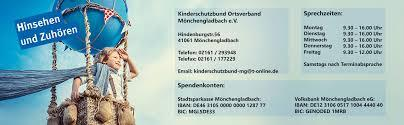
Neurnal-Network/train/MG/MG_118.jpg
