GenaroRdz/International-Power-and-Grid-Management/Neurnal-Network/train/Mini/Mini_000.jpg

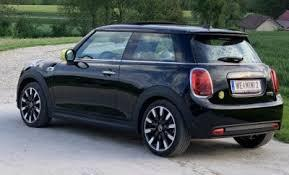
Neurnal-Network/train/Mini/Mini_000.jpg
