GenaroRdz/International-Power-and-Grid-Management/Neurnal-Network/train/Mini/Mini_004.jpg

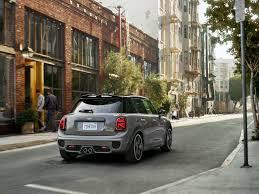
Neurnal-Network/train/Mini/Mini_004.jpg
