GenaroRdz/International-Power-and-Grid-Management/Neurnal-Network/train/Mini/Mini_009.jpg

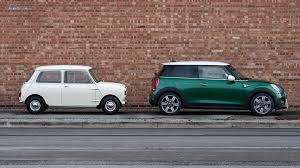
Neurnal-Network/train/Mini/Mini_009.jpg
