GenaroRdz/International-Power-and-Grid-Management/Neurnal-Network/train/Mini/Mini_015.jpg

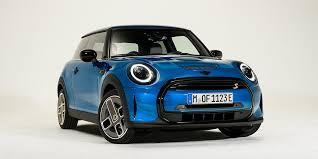
Neurnal-Network/train/Mini/Mini_015.jpg
