GenaroRdz/International-Power-and-Grid-Management/Neurnal-Network/train/Mini/Mini_024.jpg

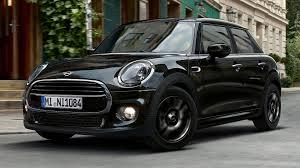
Neurnal-Network/train/Mini/Mini_024.jpg
