GenaroRdz/International-Power-and-Grid-Management/Neurnal-Network/train/Mini/Mini_039.jpg

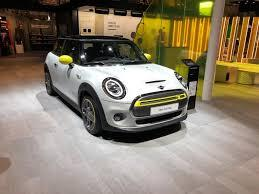
Neurnal-Network/train/Mini/Mini_039.jpg
