GenaroRdz/International-Power-and-Grid-Management/Neurnal-Network/train/Mini/Mini_048.jpg

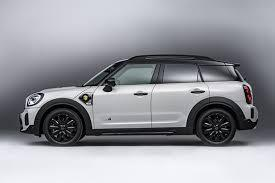
Neurnal-Network/train/Mini/Mini_048.jpg
