GenaroRdz/International-Power-and-Grid-Management/Neurnal-Network/train/Mini/Mini_073.jpg

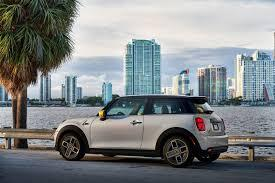
Neurnal-Network/train/Mini/Mini_073.jpg
