GenaroRdz/International-Power-and-Grid-Management/Neurnal-Network/train/Mini/Mini_084.jpg

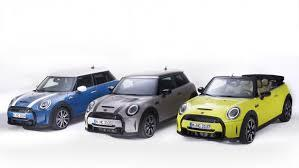
Neurnal-Network/train/Mini/Mini_084.jpg
