GenaroRdz/International-Power-and-Grid-Management/Neurnal-Network/train/Mitsubishi/Mitsubishi_029.jpg

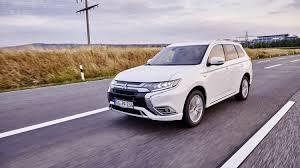
Neurnal-Network/train/Mitsubishi/Mitsubishi_029.jpg
