GenaroRdz/International-Power-and-Grid-Management/Neurnal-Network/train/Mitsubishi/Mitsubishi_054.jpg

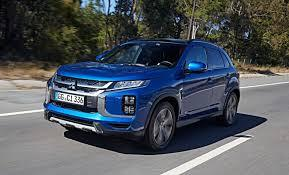
Neurnal-Network/train/Mitsubishi/Mitsubishi_054.jpg
