GenaroRdz/International-Power-and-Grid-Management/Neurnal-Network/train/Mitsubishi/Mitsubishi_061.jpg

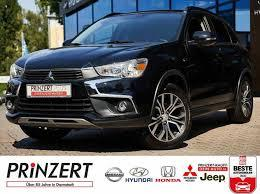
Neurnal-Network/train/Mitsubishi/Mitsubishi_061.jpg
