GenaroRdz/International-Power-and-Grid-Management/Neurnal-Network/train/Mitsubishi/Mitsubishi_073.jpg

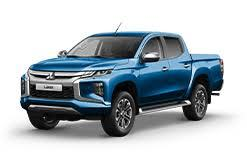
Neurnal-Network/train/Mitsubishi/Mitsubishi_073.jpg
