GenaroRdz/International-Power-and-Grid-Management/Neurnal-Network/train/Mitsubishi/Mitsubishi_075.jpg

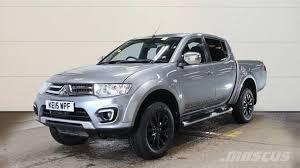
Neurnal-Network/train/Mitsubishi/Mitsubishi_075.jpg
