GenaroRdz/International-Power-and-Grid-Management/Neurnal-Network/train/Nissan/Nissan_001.jpg

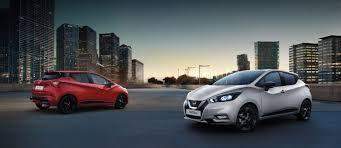
Neurnal-Network/train/Nissan/Nissan_001.jpg
