GenaroRdz/International-Power-and-Grid-Management/Neurnal-Network/train/Nissan/Nissan_003.jpg

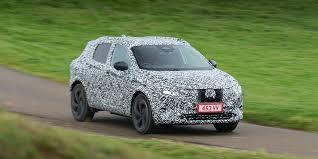
Neurnal-Network/train/Nissan/Nissan_003.jpg
