GenaroRdz/International-Power-and-Grid-Management/Neurnal-Network/train/Nissan/Nissan_010.jpg

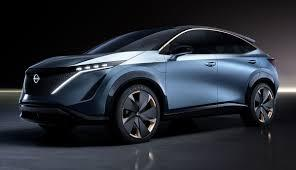
Neurnal-Network/train/Nissan/Nissan_010.jpg
