GenaroRdz/International-Power-and-Grid-Management/Neurnal-Network/train/Nissan/Nissan_044.jpg

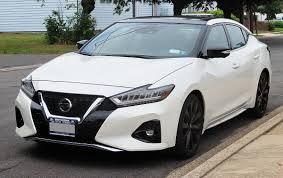
Neurnal-Network/train/Nissan/Nissan_044.jpg
