GenaroRdz/International-Power-and-Grid-Management/Neurnal-Network/train/Oldsmobile/Oldsmobile_001.jpg

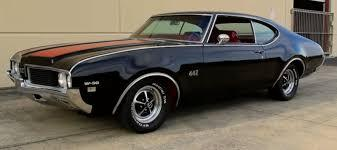
Neurnal-Network/train/Oldsmobile/Oldsmobile_001.jpg
