GenaroRdz/International-Power-and-Grid-Management/Neurnal-Network/train/Oldsmobile/Oldsmobile_030.jpg

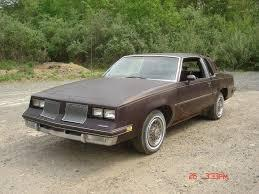
Neurnal-Network/train/Oldsmobile/Oldsmobile_030.jpg
