GenaroRdz/International-Power-and-Grid-Management/Neurnal-Network/train/Oldsmobile/Oldsmobile_055.jpg

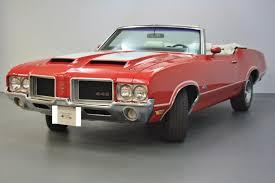
Neurnal-Network/train/Oldsmobile/Oldsmobile_055.jpg
