GenaroRdz/International-Power-and-Grid-Management/Neurnal-Network/train/Oldsmobile/Oldsmobile_065.jpg

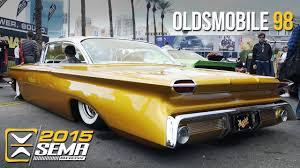
Neurnal-Network/train/Oldsmobile/Oldsmobile_065.jpg
