GenaroRdz/International-Power-and-Grid-Management/Neurnal-Network/train/Pontiac/Pontiac_010.jpg

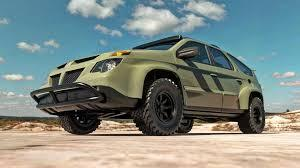
Neurnal-Network/train/Pontiac/Pontiac_010.jpg
