GenaroRdz/International-Power-and-Grid-Management/Neurnal-Network/train/Pontiac/Pontiac_014.jpg

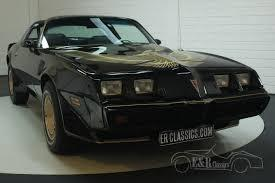
Neurnal-Network/train/Pontiac/Pontiac_014.jpg
