GenaroRdz/International-Power-and-Grid-Management/Neurnal-Network/train/Pontiac/Pontiac_029.jpg

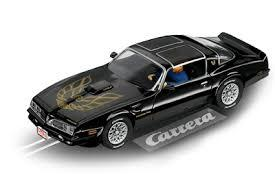
Neurnal-Network/train/Pontiac/Pontiac_029.jpg
