GenaroRdz/International-Power-and-Grid-Management/Neurnal-Network/train/Pontiac/Pontiac_043.jpg

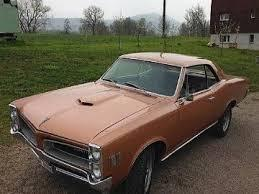
Neurnal-Network/train/Pontiac/Pontiac_043.jpg
