GenaroRdz/International-Power-and-Grid-Management/Neurnal-Network/train/Pontiac/Pontiac_045.jpg

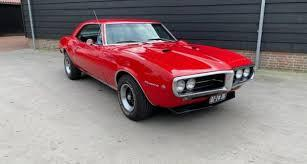
Neurnal-Network/train/Pontiac/Pontiac_045.jpg
