GenaroRdz/International-Power-and-Grid-Management/Neurnal-Network/train/Pontiac/Pontiac_054.jpg

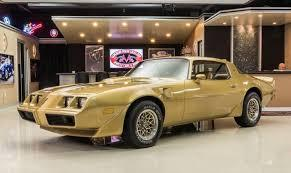
Neurnal-Network/train/Pontiac/Pontiac_054.jpg
