GenaroRdz/International-Power-and-Grid-Management/Neurnal-Network/train/Pontiac/Pontiac_071.jpg

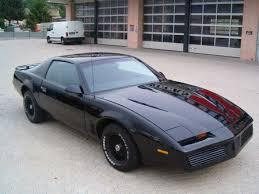
Neurnal-Network/train/Pontiac/Pontiac_071.jpg
