GenaroRdz/International-Power-and-Grid-Management/Neurnal-Network/train/Pontiac/Pontiac_073.jpg

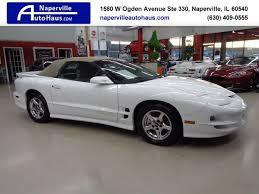
Neurnal-Network/train/Pontiac/Pontiac_073.jpg
