GenaroRdz/International-Power-and-Grid-Management/Neurnal-Network/train/Pontiac/Pontiac_093.jpg

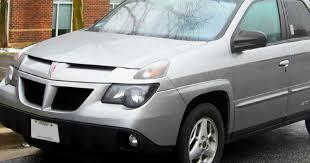
Neurnal-Network/train/Pontiac/Pontiac_093.jpg
