GenaroRdz/International-Power-and-Grid-Management/Neurnal-Network/train/Porsche/Porsche_006.jpg

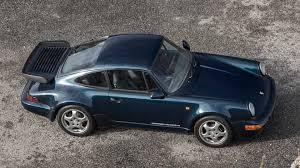
Neurnal-Network/train/Porsche/Porsche_006.jpg
