GenaroRdz/International-Power-and-Grid-Management/Neurnal-Network/train/Porsche/Porsche_014.jpg

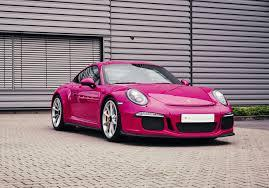
Neurnal-Network/train/Porsche/Porsche_014.jpg
