GenaroRdz/International-Power-and-Grid-Management/Neurnal-Network/train/Porsche/Porsche_019.jpg

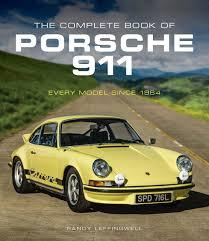
Neurnal-Network/train/Porsche/Porsche_019.jpg
