GenaroRdz/International-Power-and-Grid-Management/Neurnal-Network/train/Porsche/Porsche_032.jpg

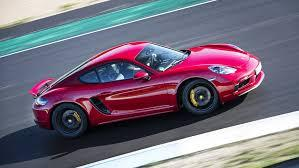
Neurnal-Network/train/Porsche/Porsche_032.jpg
