GenaroRdz/International-Power-and-Grid-Management/Neurnal-Network/train/Porsche/Porsche_058.jpg

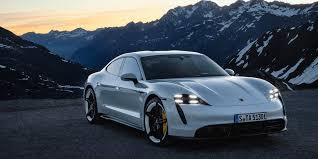
Neurnal-Network/train/Porsche/Porsche_058.jpg
