GenaroRdz/International-Power-and-Grid-Management/Neurnal-Network/train/Porsche/Porsche_085.jpg

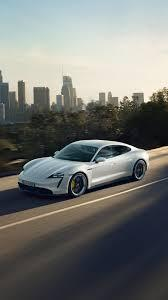
Neurnal-Network/train/Porsche/Porsche_085.jpg
