GenaroRdz/International-Power-and-Grid-Management/Neurnal-Network/train/Ram Trucks/Ram Trucks_013.jpg

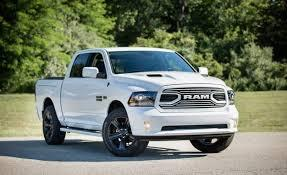
Neurnal-Network/train/Ram Trucks/Ram Trucks_013.jpg
