GenaroRdz/International-Power-and-Grid-Management/Neurnal-Network/train/Ram Trucks/Ram Trucks_020.jpg

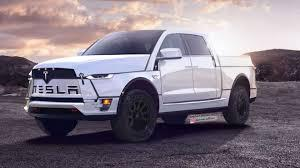
Neurnal-Network/train/Ram Trucks/Ram Trucks_020.jpg
