GenaroRdz/International-Power-and-Grid-Management/Neurnal-Network/train/Ram Trucks/Ram Trucks_044.jpg

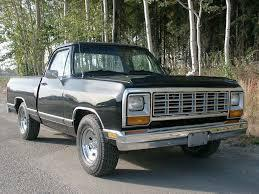
Neurnal-Network/train/Ram Trucks/Ram Trucks_044.jpg
