GenaroRdz/International-Power-and-Grid-Management/Neurnal-Network/train/Ram Trucks/Ram Trucks_053.jpg

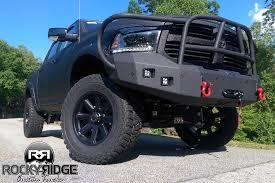
Neurnal-Network/train/Ram Trucks/Ram Trucks_053.jpg
