GenaroRdz/International-Power-and-Grid-Management/Neurnal-Network/train/Ram Trucks/Ram Trucks_069.jpg

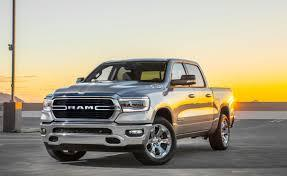
Neurnal-Network/train/Ram Trucks/Ram Trucks_069.jpg
