GenaroRdz/International-Power-and-Grid-Management/Neurnal-Network/train/Ram Trucks/Ram Trucks_074.jpg

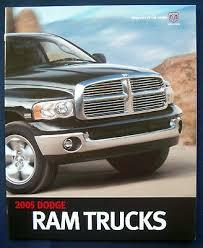
Neurnal-Network/train/Ram Trucks/Ram Trucks_074.jpg
