GenaroRdz/International-Power-and-Grid-Management/Neurnal-Network/train/Renault/Renault_002.jpg

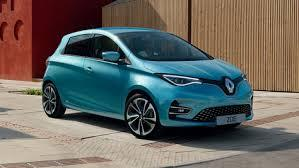
Neurnal-Network/train/Renault/Renault_002.jpg
