GenaroRdz/International-Power-and-Grid-Management/Neurnal-Network/train/Renault/Renault_017.jpg

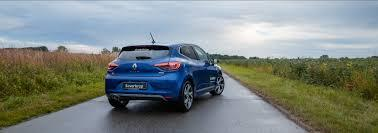
Neurnal-Network/train/Renault/Renault_017.jpg
