GenaroRdz/International-Power-and-Grid-Management/Neurnal-Network/train/Renault/Renault_027.jpg

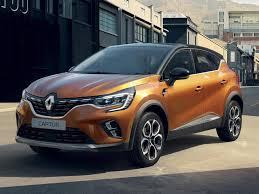
Neurnal-Network/train/Renault/Renault_027.jpg
