GenaroRdz/International-Power-and-Grid-Management/Neurnal-Network/train/Renault/Renault_035.jpg

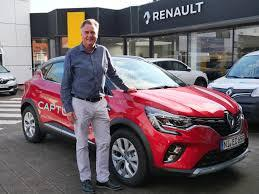
Neurnal-Network/train/Renault/Renault_035.jpg
