GenaroRdz/International-Power-and-Grid-Management/Neurnal-Network/train/Renault/Renault_051.jpg

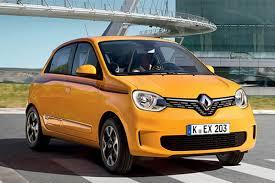
Neurnal-Network/train/Renault/Renault_051.jpg
