GenaroRdz/International-Power-and-Grid-Management/Neurnal-Network/train/Saab/Saab_017.jpg

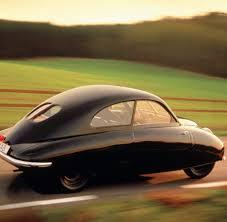
Neurnal-Network/train/Saab/Saab_017.jpg
