GenaroRdz/International-Power-and-Grid-Management/Neurnal-Network/train/Saab/Saab_022.jpg

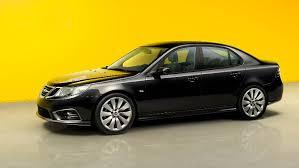
Neurnal-Network/train/Saab/Saab_022.jpg
