GenaroRdz/International-Power-and-Grid-Management/Neurnal-Network/train/Saab/Saab_028.jpg

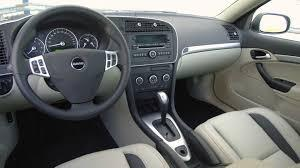
Neurnal-Network/train/Saab/Saab_028.jpg
