GenaroRdz/International-Power-and-Grid-Management/Neurnal-Network/train/Saab/Saab_058.jpg

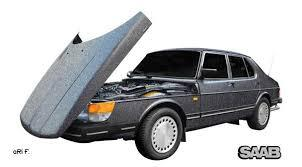
Neurnal-Network/train/Saab/Saab_058.jpg
