GenaroRdz/International-Power-and-Grid-Management/Neurnal-Network/train/Studebaker/Studebaker_013.jpg

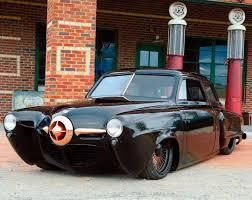
Neurnal-Network/train/Studebaker/Studebaker_013.jpg
