GenaroRdz/International-Power-and-Grid-Management/Neurnal-Network/train/Studebaker/Studebaker_059.jpg

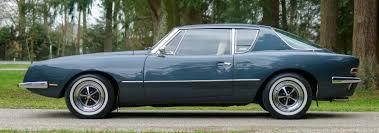
Neurnal-Network/train/Studebaker/Studebaker_059.jpg
