GenaroRdz/International-Power-and-Grid-Management/Neurnal-Network/train/Studebaker/Studebaker_078.jpg

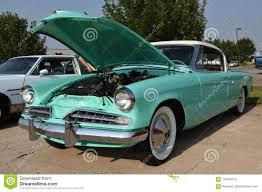
Neurnal-Network/train/Studebaker/Studebaker_078.jpg
