GenaroRdz/International-Power-and-Grid-Management/Neurnal-Network/train/Studebaker/Studebaker_084.jpg

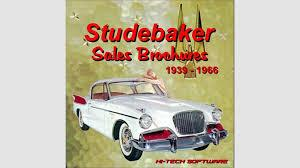
Neurnal-Network/train/Studebaker/Studebaker_084.jpg
