GenaroRdz/International-Power-and-Grid-Management/Neurnal-Network/train/Subaru/Subaru_008.jpg

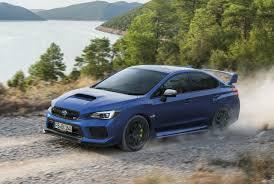
Neurnal-Network/train/Subaru/Subaru_008.jpg
