GenaroRdz/International-Power-and-Grid-Management/Neurnal-Network/train/Subaru/Subaru_049.jpg

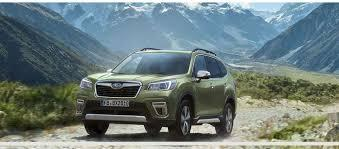
Neurnal-Network/train/Subaru/Subaru_049.jpg
