GenaroRdz/International-Power-and-Grid-Management/Neurnal-Network/train/Subaru/Subaru_055.jpg

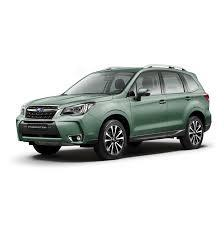
Neurnal-Network/train/Subaru/Subaru_055.jpg
