GenaroRdz/International-Power-and-Grid-Management/Neurnal-Network/train/Subaru/Subaru_072.jpg

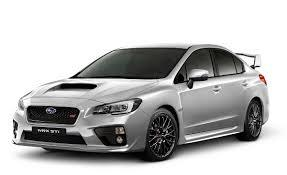
Neurnal-Network/train/Subaru/Subaru_072.jpg
