GenaroRdz/International-Power-and-Grid-Management/Neurnal-Network/train/Subaru/Subaru_079.jpg

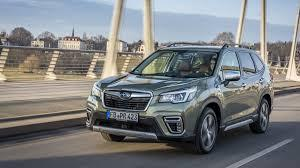
Neurnal-Network/train/Subaru/Subaru_079.jpg
