GenaroRdz/International-Power-and-Grid-Management/Neurnal-Network/train/Suzuki/Suzuki_001.jpg

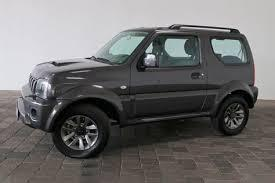
Neurnal-Network/train/Suzuki/Suzuki_001.jpg
