GenaroRdz/International-Power-and-Grid-Management/Neurnal-Network/train/Suzuki/Suzuki_002.jpg

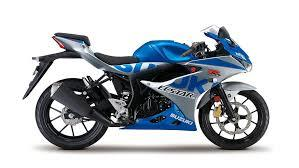
Neurnal-Network/train/Suzuki/Suzuki_002.jpg
