GenaroRdz/International-Power-and-Grid-Management/Neurnal-Network/train/Suzuki/Suzuki_004.jpg

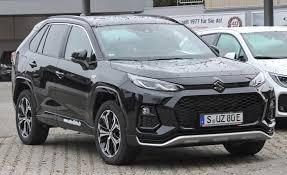
Neurnal-Network/train/Suzuki/Suzuki_004.jpg
