GenaroRdz/International-Power-and-Grid-Management/Neurnal-Network/train/Suzuki/Suzuki_021.jpg

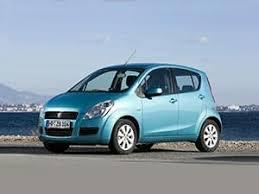
Neurnal-Network/train/Suzuki/Suzuki_021.jpg
