GenaroRdz/International-Power-and-Grid-Management/Neurnal-Network/train/Suzuki/Suzuki_032.jpg

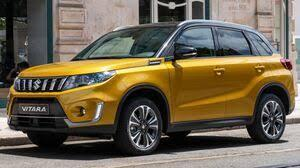
Neurnal-Network/train/Suzuki/Suzuki_032.jpg
