GenaroRdz/International-Power-and-Grid-Management/Neurnal-Network/train/Suzuki/Suzuki_036.jpg

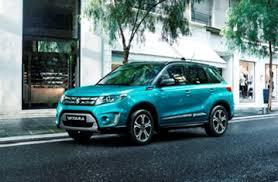
Neurnal-Network/train/Suzuki/Suzuki_036.jpg
