GenaroRdz/International-Power-and-Grid-Management/Neurnal-Network/train/Suzuki/Suzuki_052.jpg

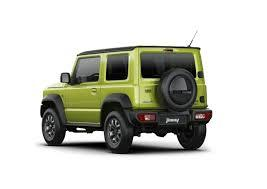
Neurnal-Network/train/Suzuki/Suzuki_052.jpg
