GenaroRdz/International-Power-and-Grid-Management/Neurnal-Network/train/Suzuki/Suzuki_059.jpg

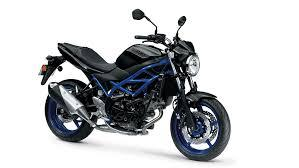
Neurnal-Network/train/Suzuki/Suzuki_059.jpg
