GenaroRdz/International-Power-and-Grid-Management/Neurnal-Network/train/Tesla/Tesla_016.jpg

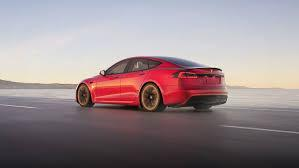
Neurnal-Network/train/Tesla/Tesla_016.jpg
