GenaroRdz/International-Power-and-Grid-Management/Neurnal-Network/train/Tesla/Tesla_042.jpg

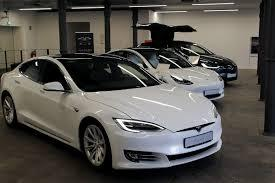
Neurnal-Network/train/Tesla/Tesla_042.jpg
