GenaroRdz/International-Power-and-Grid-Management/Neurnal-Network/train/Tesla/Tesla_043.jpg

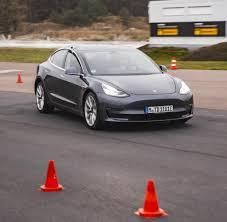
Neurnal-Network/train/Tesla/Tesla_043.jpg
