GenaroRdz/International-Power-and-Grid-Management/Neurnal-Network/train/Tesla/Tesla_044.jpg

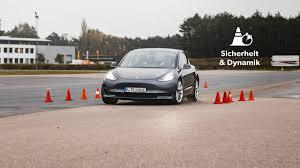
Neurnal-Network/train/Tesla/Tesla_044.jpg
