GenaroRdz/International-Power-and-Grid-Management/Neurnal-Network/train/Tesla/Tesla_054.jpg

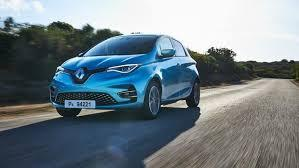
Neurnal-Network/train/Tesla/Tesla_054.jpg
