GenaroRdz/International-Power-and-Grid-Management/Neurnal-Network/train/Tesla/Tesla_055.jpg

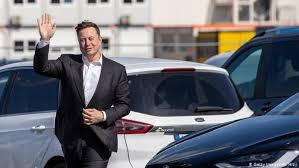
Neurnal-Network/train/Tesla/Tesla_055.jpg
