GenaroRdz/International-Power-and-Grid-Management/Neurnal-Network/train/Tesla/Tesla_071.jpg

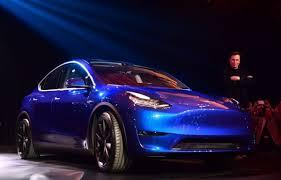
Neurnal-Network/train/Tesla/Tesla_071.jpg
