GenaroRdz/International-Power-and-Grid-Management/Neurnal-Network/train/Tesla/Tesla_075.jpg

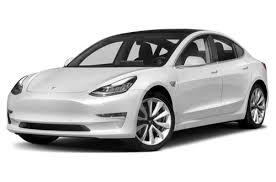
Neurnal-Network/train/Tesla/Tesla_075.jpg
