GenaroRdz/International-Power-and-Grid-Management/Neurnal-Network/train/Tesla/Tesla_086.jpg

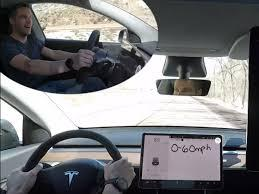
Neurnal-Network/train/Tesla/Tesla_086.jpg
