GenaroRdz/International-Power-and-Grid-Management/Neurnal-Network/train/Tesla/Tesla_087.jpg

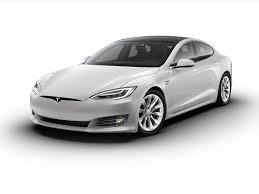
Neurnal-Network/train/Tesla/Tesla_087.jpg
