GenaroRdz/International-Power-and-Grid-Management/Neurnal-Network/train/Toyota/Toyota_003.jpg

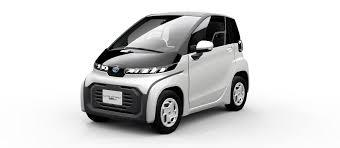
Neurnal-Network/train/Toyota/Toyota_003.jpg
