GenaroRdz/International-Power-and-Grid-Management/Neurnal-Network/train/Toyota/Toyota_018.jpg

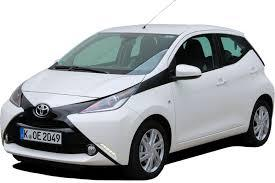
Neurnal-Network/train/Toyota/Toyota_018.jpg
