GenaroRdz/International-Power-and-Grid-Management/Neurnal-Network/train/Toyota/Toyota_028.jpg

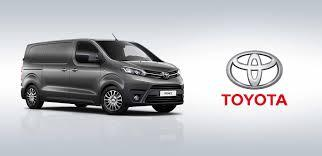
Neurnal-Network/train/Toyota/Toyota_028.jpg
