GenaroRdz/International-Power-and-Grid-Management/Neurnal-Network/train/Volkswagen/Volkswagen_040.jpg

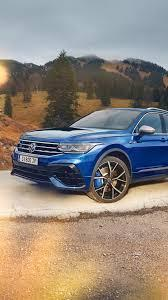
Neurnal-Network/train/Volkswagen/Volkswagen_040.jpg
