GenaroRdz/International-Power-and-Grid-Management/Neurnal-Network/train/Volkswagen/Volkswagen_047.jpg

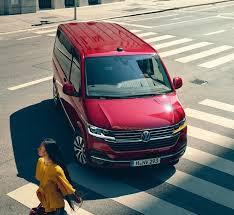
Neurnal-Network/train/Volkswagen/Volkswagen_047.jpg
