GenaroRdz/International-Power-and-Grid-Management/Neurnal-Network/train/Volkswagen/Volkswagen_080.jpg

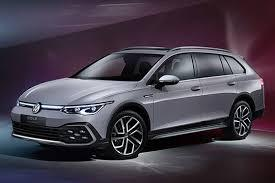
Neurnal-Network/train/Volkswagen/Volkswagen_080.jpg
