GenaroRdz/International-Power-and-Grid-Management/Neurnal-Network/train/Volkswagen/Volkswagen_086.jpg

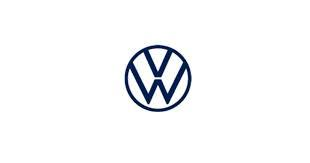
Neurnal-Network/train/Volkswagen/Volkswagen_086.jpg
