GenaroRdz/International-Power-and-Grid-Management/Neurnal-Network/train/Volvo/Volvo_005.jpg

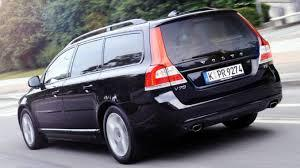
Neurnal-Network/train/Volvo/Volvo_005.jpg
