GenaroRdz/International-Power-and-Grid-Management/Neurnal-Network/train/Volvo/Volvo_009.jpg

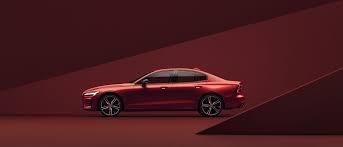
Neurnal-Network/train/Volvo/Volvo_009.jpg
