GenaroRdz/International-Power-and-Grid-Management/Neurnal-Network/train/Volvo/Volvo_034.jpg

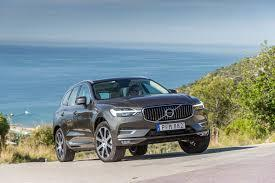
Neurnal-Network/train/Volvo/Volvo_034.jpg
