GenaroRdz/International-Power-and-Grid-Management/Neurnal-Network/train/Volvo/Volvo_056.jpg

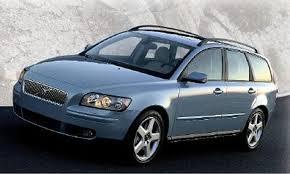
Neurnal-Network/train/Volvo/Volvo_056.jpg
