GenaroRdz/International-Power-and-Grid-Management/Neurnal-Network/train/Volvo/Volvo_058.jpg

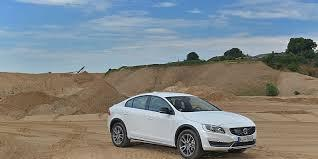
Neurnal-Network/train/Volvo/Volvo_058.jpg
