GenaroRdz/International-Power-and-Grid-Management/Neurnal-Network/train/Volvo/Volvo_072.jpg

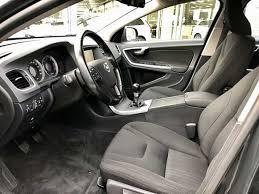
Neurnal-Network/train/Volvo/Volvo_072.jpg
