GenaroRdz/International-Power-and-Grid-Management/hardware/LTspice_simulations/International_v1.asc

D1: schottky; 1N5408
D2: schottky; 1N5408
D3: schottky; 1N5408
D4: schottky; 1N5408
M1: pmos; IRF4905
M2: pmos; IRF4905
M3: pmos; IRF4905
M4: pmos; IRF4905
R1: res; 10k
R2: res; 10k
R3: res; 10k
R4: res; 10k
R5: res; 330
R6: res; 330
R7: res; 330
R8: res; 330
R9: res; 2.4
R10: res; 2.4
R11: res; 2.4
R12: res; 2.4
R13: res; 50m
R14: res; 50m
R15: res; 50m
R16: res; 50m
U1: PC817B
U2: PC817B
U3: PC817B
U4: PC817B
V1: voltage; PULSE(0 3.3 0 1n 0 10m 20m)
V2: voltage; 12
Named nets: 0
.tran 0.1
.model IRF4905 VDMOS(pchan Vto=-4.0 Rds=0.02 Kp=40 Cgs=3n Cgdmax=2n)
.model 1N5408 D(IS=5e-08 RS=0.044 N=1.5 BV=1000 IBV=5e-08 CJO=4e-11 TT=3e-06)
